Jsmaldo/Keyboard-PCB/Aliexpress slide pot/pic2.PNG

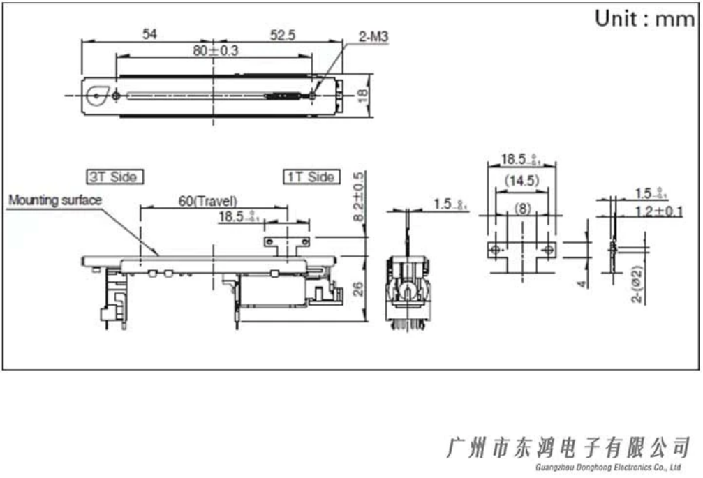
Aliexpress slide pot/pic2.PNG
