Jsmaldo/Keyboard-PCB/Firmware & SourceCode (unofficial)/Wiring Layout.PNG

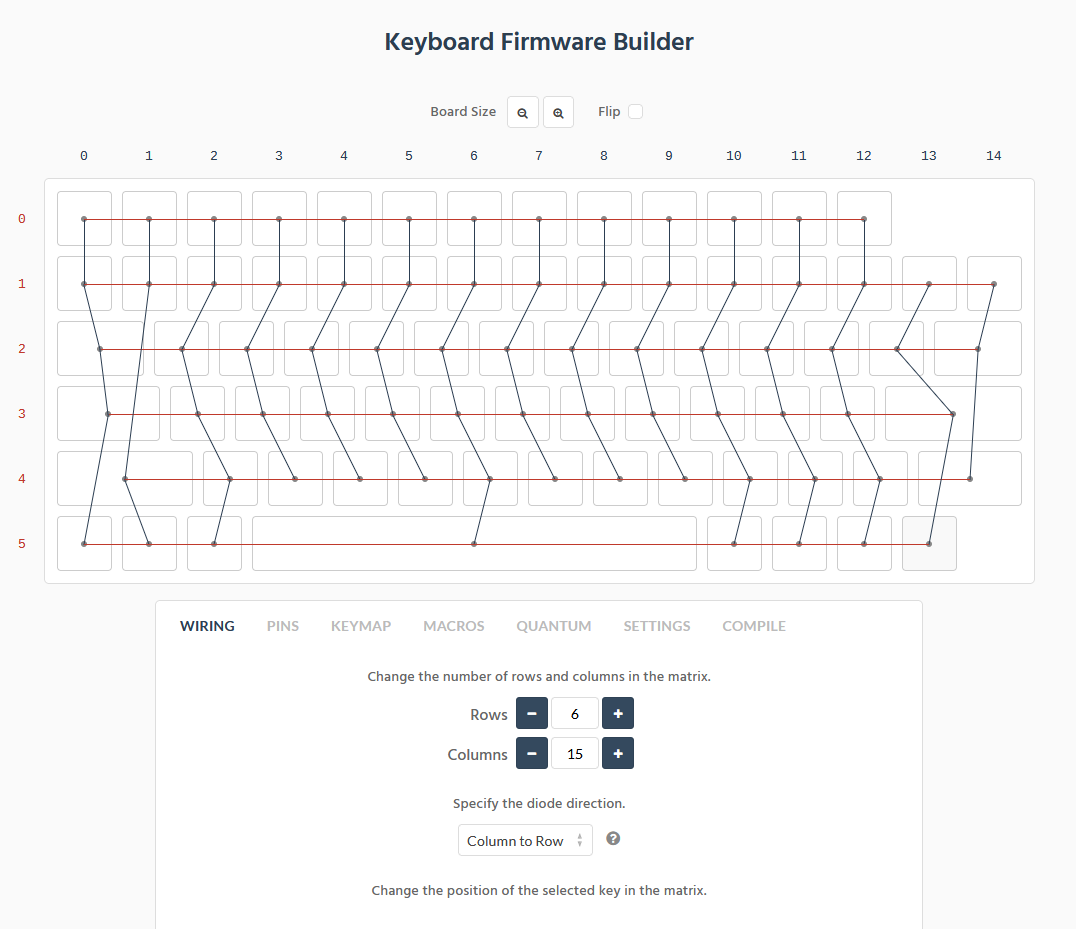
Firmware & SourceCode (unofficial)/Wiring Layout.PNG
